jsphuebner/FlyingAdcBms/src/bmsio.cpp

/*
 * This file is part of the FlyingADCBMS project.
 *
 * Copyright (C) 2025 Johannes Huebner <dev@johanneshuebner.com>
 *
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
 * You should have received a copy of the GNU General Public License
 * along with this program.  If not, see <http://www.gnu.org/licenses/>.
 */
#include "bmsio.h"
#include "params.h"
#include "anain.h"
#include "temp_meas.h"
#include "my_math.h"
#include "flyingadcbms.h"

BmsFsm* BmsIO::bmsFsm;
int BmsIO::muxRequest = -1;

/** \brief Mux control function. Must be called in 2 ms interval */
void BmsIO::SwitchMux()
{
   static int channel = -1;
   static bool startAdc = false;

   //t=0 ms: On a mux change request first completely turn off mux
   if (muxRequest >= 0)
   {
      FlyingAdcBms::MuxOff();
      channel = muxRequest;
      muxRequest = -1;
   }
   //t=2 ms: switch to requested channel
   else if (channel >= 0)
   {
      FlyingAdcBms::SelectChannel(channel);
      channel = -1;
      startAdc = true;
   }
   //t=4 ms: start ADC
   else if (startAdc)
   {
      FlyingAdcBms::StartAdc();
      startAdc = false;
   }
   //t=21 ms: ADC conversion is finished
   //t=25 ms: ADC conversion result is read
}

void BmsIO::ReadCellVoltages()
{
   const int totalBalanceCycles = 30;
   static uint8_t chan = 0, balanceCycles = 0;
   static float sum = 0, min = 8000, max = 0;
   int balMode = Param::GetInt(Param::balmode);
   bool balance = Param::GetInt(Param::opmode) == BmsFsm::IDLE && Param::GetFloat(Param::uavg) > Param::GetFloat(Param::ubalance) && BAL_OFF != balMode;
   FlyingAdcBms::BalanceStatus bstt;

   if (balance)
   {
      float balanceMax = Param::GetFloat(Param::ucell100soc);
      if (balanceCycles == 0)
      {
         balanceCycles = totalBalanceCycles; //this leads to switching to next channel below
      }
      else
      {
         balanceCycles--;
      }

      if (balanceCycles > 0 && balanceCycles < (totalBalanceCycles - 1))
      {
         float udc = Param::GetFloat((Param::PARAM_NUM)(Param::u0 + chan));
         float balanceTarget = 0;

         switch (balMode)
         {
         case BAL_ADD: //maximum cell voltage is target when only adding
            balanceTarget = Param::GetFloat(Param::umax);
            break;
         case BAL_DIS: //minimum cell voltage is target when only dissipating
            balanceTarget = Param::GetFloat(Param::umin);
            break;
         case BAL_BOTH: //average cell voltage is target when dissipating and adding
            balanceTarget = Param::GetFloat(Param::uavg);
            break;
         default: //not balancing
            break;
         }

         balanceTarget = MIN(balanceTarget, balanceMax);

         if (udc < (balanceTarget - 3) && (balMode & BAL_ADD))
         {
            bstt = FlyingAdcBms::SetBalancing(FlyingAdcBms::BAL_CHARGE);
         }
         else if (udc > (balanceTarget + 1) && (balMode & BAL_DIS))
         {
            bstt = FlyingAdcBms::SetBalancing(FlyingAdcBms::BAL_DISCHARGE);
         }
         else
         {
            bstt = FlyingAdcBms::SetBalancing(FlyingAdcBms::BAL_OFF);
            balanceCycles = 0;
         }
         Param::SetInt((Param::PARAM_NUM)(Param::u0cmd + chan), bstt);
      }
      else
      {
         FlyingAdcBms::SetBalancing(FlyingAdcBms::BAL_OFF);
      }
   }
   else
   {
      balanceCycles = totalBalanceCycles;
      bstt = FlyingAdcBms::SetBalancing(FlyingAdcBms::BAL_OFF);
      Param::SetInt((Param::PARAM_NUM)(Param::u0cmd + chan), bstt);
   }

   //Read cell voltage when balancing is turned off
   if (balanceCycles == totalBalanceCycles)
   {
      float gain = Param::GetFloat(Param::gain);
      int numChan = Param::GetInt(Param::numchan);
      bool even = (chan & 1) == 0;

      if (chan == 0)
         gain *= 1 + Param::GetFloat(Param::correction0) / 1000000.0f;
      else if (chan == 1)
         gain *= 1 + Param::GetFloat(Param::correction1) / 1000000.0f;
      else if (chan == 15)
         gain *= 1 + Param::GetFloat(Param::correction15) / 1000000.0f;

      //Read ADC result before mux change
      float udc = FlyingAdcBms::GetResult() * (gain / 1000.0f);

      Param::SetFloat((Param::PARAM_NUM)(Param::u0 + chan), udc);

      min = MIN(min, udc);
      max = MAX(max, udc);
      sum += udc;

      //First we sweep across all even channels: 0, 2, 4,...
      if (even && (chan + 2) < numChan)
         chan += 2;
      //After reaching the furthest even channel (say 12) we either change over to a higher odd channel
      else if (even && (chan + 1) < numChan)
         chan++;
      //or lower odd channel
      else if (even)
         chan--;
      //Now we sweep across all odd channels until we reach 1
      else if (chan > 1)
         chan -= 2;
      //We have now reached chan 1. Accumulate values and restart at chan 0
      else
      {
         chan = 0;
         Accumulate(sum, min, max, sum / numChan);

         min = 8000;
         max = 0;
         sum = 0;
      }
      //This instructs the SwitchMux task to change channel, with dead time
      muxRequest = chan;
   }
}

void BmsIO::ReadTemperatures()
{
   int sensor = Param::GetInt(Param::tempsns);
   int nomRes = Param::GetInt(Param::tempres);
   int beta = Param::GetInt(Param::tempbeta);
   float temp1 = NO_TEMP, temp2 = NO_TEMP, tempmin = NO_TEMP, tempmax = NO_TEMP;

   if (sensor & 1)
      tempmin = tempmax = temp1 = TempMeas::AdcToTemperature(AnaIn::temp1.Get(), nomRes, beta);

   if (sensor & 2)
      tempmin = tempmax = temp2 = TempMeas::AdcToTemperature(AnaIn::temp2.Get(), nomRes, beta);

   if (sensor == 3) //two sensors, calculate min and max
   {
      tempmin = MIN(temp1, temp2);
      tempmax = MAX(temp1, temp2);
   }

   Param::SetFloat(Param::tempmin0, tempmin);
   Param::SetFloat(Param::tempmax0, tempmax);
}

void BmsIO::MeasureCurrent()
{
   int idcmode = Param::GetInt(Param::idcmode);

   if (idcmode == IDC_DIFFERENTIAL || idcmode == IDC_SINGLE)
   {
      float current = 0;
      static int samples = 0;
      static u32fp amsIn = 0, amsOut = 0;
      static float idcavg = 0;
      int curpos = AnaIn::curpos.Get();
      int curneg = AnaIn::curneg.Get();
      float idcgain = Param::GetFloat(Param::idcgain);
      int idcofs = Param::GetInt(Param::idcofs);
      int rawCurrent = idcmode == IDC_SINGLE ? curpos : curpos - curneg;

      current = (rawCurrent - idcofs) / idcgain;

      if (current < -Param::GetFloat(Param::idlethresh))
      {
         amsOut += -FP_FROMFLT(current);
      }
      else if (current > Param::GetFloat(Param::idlethresh))
      {
         amsIn += FP_FROMFLT(current);
      }

      idcavg += current;
      samples++;

      if (samples == 200)
      {
         s32fp chargein = Param::Get(Param::chargein);
         s32fp chargeout = Param::Get(Param::chargeout);

         chargein += amsIn / 200;
         chargeout += amsOut / 200;
         idcavg /= 200;

         float voltage = Param::GetFloat(Param::utotal) / 1000;
         float power = voltage * idcavg;

         Param::SetFloat(Param::idcavg, idcavg);
         Param::SetFloat(Param::power, power);

         amsIn = 0;
         amsOut = 0;
         samples = 0;
         idcavg = 0;

         //BmsCalculation::SetCharge(chargein, chargeout);
         Param::SetFixed(Param::chargein, chargein);
         Param::SetFixed(Param::chargeout, chargeout);
      }
      Param::SetFloat(Param::idc, current);
   }
}

void BmsIO::TestReadCellVoltage(int chan, FlyingAdcBms::BalanceCommand cmd)
{
   float gain = Param::GetFloat(Param::gain);

   if (chan == 0)
      gain *= 1 + Param::GetFloat(Param::correction0) / 1000000.0f;
   else if (chan == 1)
      gain *= 1 + Param::GetFloat(Param::correction1) / 1000000.0f;
   else if (chan == 15)
      gain *= 1 + Param::GetFloat(Param::correction15) / 1000000.0f;

   float udc = FlyingAdcBms::GetResult() * (gain / 1000.0f);;
   FlyingAdcBms::SelectChannel(chan);
   FlyingAdcBms::SetBalancing(cmd);
   FlyingAdcBms::StartAdc();
   Param::SetFloat((Param::PARAM_NUM)(Param::u0 + chan), udc);
}

void BmsIO::Accumulate(float sum, float min, float max, float avg)
{
   if (bmsFsm->IsFirst())
   {
      Param::SetFloat(Param::uavg0, avg);
      Param::SetFloat(Param::umin0, min);
      Param::SetFloat(Param::umax0, max);

      float totalSum = sum, totalMin = min, totalMax = max;
      //If we are the first module accumulate our values with those from the sub modules
      for (int i = 1; i < bmsFsm->GetNumberOfModules(); i++)
      {
         //Here we undo the local average calculation on the module to calculate the substrings total voltage
         totalSum += Param::GetFloat(bmsFsm->GetDataItem(Param::uavg0, i)) * bmsFsm->GetCellsOfModule(i);
         totalMin = MIN(totalMin, Param::GetFloat(bmsFsm->GetDataItem(Param::umin0, i)));
         totalMax = MAX(totalMax, Param::GetFloat(bmsFsm->GetDataItem(Param::umax0, i)));
      }

      float tempmin = NO_TEMP, tempmax = -40;

      for (int i = 0; i < bmsFsm->GetNumberOfModules(); i++)
      {
         float tempmin0 = Param::GetFloat(bmsFsm->GetDataItem(Param::tempmin0, i));
         float tempmax0 = Param::GetFloat(bmsFsm->GetDataItem(Param::tempmax0, i));

         if (tempmin0 < NO_TEMP)
         {
            tempmin = MIN(tempmin, tempmin0);
            tempmax = MAX(tempmax, tempmax0);
         }
      }

      Param::SetFloat(Param::umin, totalMin);
      Param::SetFloat(Param::umax, totalMax);
      Param::SetFloat(Param::uavg, totalSum / Param::GetInt(Param::totalcells));
      Param::SetFloat(Param::udelta, totalMax - totalMin);
      Param::SetFloat(Param::utotal, totalSum);
      Param::SetFloat(Param::tempmin, tempmin);
      Param::SetFloat(Param::tempmax, tempmax);
   }
   else //if we are a sub module write averages straight to data module
   {
      Param::SetFloat(Param::utotal, sum);
      Param::SetFloat(Param::uavg0, avg);
      Param::SetFloat(Param::umin0, min);
      Param::SetFloat(Param::umax0, max);
      Param::SetFloat(Param::udelta, max - min);
   }
}
